noahlessard/2040Listener/main_host.c

/*
 * The MIT License (MIT)
 *
 * Copyright (c) 2019 Ha Thach (tinyusb.org)
 *                    sekigon-gonnoc
 *
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
 */

// This example runs both host and device concurrently. The USB host receive
// reports from HID device and print it out over USB Device CDC interface.
// For TinyUSB roothub port0 is native usb controller, roothub port1 is
// pico-pio-usb.

#include <stdlib.h>
#include <stdio.h>
#include <string.h>

#include "pico/stdlib.h"
#include "pico/multicore.h"
#include "pico/bootrom.h"

#include "pio_usb.h"
#include "tusb.h"
#include "usb_descriptors.h"
#include "pico_lfs.h"

#include "pico/util/queue.h"



//--------------------------------------------------------------------+
// MACRO CONSTANT TYPEDEF PROTYPES
//--------------------------------------------------------------------+


volatile bool core1_ready = false;
static uint8_t const keycode2ascii[128][2] =  { HID_KEYCODE_TO_ASCII };
extern queue_t keypress_queue;

/*------------- MAIN -------------*/

// core1: handle host events
void core1_main() {
  sleep_ms(10);

  // need to allow this core to be paused by core0! Otherwise LFS won't work
  multicore_lockout_victim_init();
  core1_ready = true;  

  // Use tuh_configure() to pass pio configuration to the host stack
  // Note: tuh_configure() must be called before
  pio_usb_configuration_t pio_cfg = {
    .pin_dp = PIO_USB_DP_PIN_DEFAULT,
    .pio_tx_num = PIO_USB_TX_DEFAULT,
    .sm_tx = PIO_SM_USB_TX_DEFAULT,
    .tx_ch = PIO_USB_DMA_TX_DEFAULT,
    .pio_rx_num = PIO_USB_RX_DEFAULT,
    .sm_rx = PIO_SM_USB_RX_DEFAULT,
    .sm_eop = PIO_SM_USB_EOP_DEFAULT,
    .alarm_pool = NULL, // Set to your alarm pool if you have one, otherwise NULL
    .debug_pin_rx = PIO_USB_DEBUG_PIN_NONE,
    .debug_pin_eop = PIO_USB_DEBUG_PIN_NONE,
    .skip_alarm_pool = false, // Add this line, typically false if using alarm_pool
    .pinout = PIO_USB_PINOUT_DPDM // Add this line, as per newer pio_usb.h
};
  tuh_configure(1, TUH_CFGID_RPI_PIO_USB_CONFIGURATION, &pio_cfg);

  // To run USB SOF interrupt in core1, init host stack for pio_usb (roothub
  // port1) on core1
  tuh_init(1);

  while (true) {
    tuh_task(); // tinyusb host task, process all data coming from keyboard
  }
}

//--------------------------------------------------------------------+
// Host HID
//--------------------------------------------------------------------+

// Invoked when device with hid interface is mounted
// Report descriptor is also available for use. tuh_hid_parse_report_descriptor()
// can be used to parse common/simple enough descriptor.
// Note: if report descriptor length > CFG_TUH_ENUMERATION_BUFSIZE, it will be skipped
// therefore report_desc = NULL, desc_len = 0
void tuh_hid_mount_cb(uint8_t dev_addr, uint8_t instance, uint8_t const* desc_report, uint16_t desc_len)
{
  (void)desc_report;
  (void)desc_len;

  // Interface protocol (hid_interface_protocol_enum_t)
  const char* protocol_str[] = { "None", "Keyboard", "Mouse" };
  uint8_t const itf_protocol = tuh_hid_interface_protocol(dev_addr, instance);

  uint16_t vid, pid;
  tuh_vid_pid_get(dev_addr, &vid, &pid);

  char tempbuf[256];
  int count = sprintf(tempbuf, "[%04x:%04x][%u] HID Interface%u, Protocol = %s\r\n", vid, pid, dev_addr, instance, protocol_str[itf_protocol]);

  tud_cdc_write(tempbuf, count);
  tud_cdc_write_flush();

  // Receive report from boot keyboard & mouse only
  // tuh_hid_report_received_cb() will be invoked when report is available
  if (itf_protocol == HID_ITF_PROTOCOL_KEYBOARD || itf_protocol == HID_ITF_PROTOCOL_MOUSE)
  {
    if ( !tuh_hid_receive_report(dev_addr, instance) )
    {
      tud_cdc_write_str("Error: cannot request report\r\n");
    }
  }
}

// Invoked when device with hid interface is un-mounted
void tuh_hid_umount_cb(uint8_t dev_addr, uint8_t instance)
{
  char tempbuf[256];
  int count = sprintf(tempbuf, "[%u] HID Interface%u is unmounted\r\n", dev_addr, instance);
  tud_cdc_write(tempbuf, count);
  tud_cdc_write_flush();
}

// look up new key in previous keys
static inline bool find_key_in_report(hid_keyboard_report_t const *report, uint8_t keycode)
{
  for(uint8_t i=0; i<6; i++)
  {
    if (report->keycode[i] == keycode)  return true;
  }

  return false;
}


// convert hid keycode to ascii and print via usb device CDC (ignore non-printable)
static void process_kbd_report(uint8_t dev_addr, hid_keyboard_report_t const *report)
{
  (void) dev_addr;
  static hid_keyboard_report_t prev_report = { 0, 0, {0} }; // previous report to check key released
  bool flush = false;

  // send keyboard report data to real host, via tud task (which is in core0)
  tud_hid_keyboard_report(REPORT_ID_KEYBOARD, report->modifier, (uint8_t*) report->keycode);
  
  for(uint8_t i=0; i<6; i++)
  {
    uint8_t keycode = report->keycode[i];
    if ( keycode )
    {
      if ( find_key_in_report(&prev_report, keycode) )
      {
        // exist in previous report means the current key is holding
      }else
      {
        // not existed in previous report means the current key is pressed

        bool const is_shift = report->modifier & (KEYBOARD_MODIFIER_LEFTSHIFT | KEYBOARD_MODIFIER_RIGHTSHIFT);
        uint8_t ch = keycode2ascii[keycode][is_shift ? 1 : 0];

        if (ch)
        {
          queue_try_add(&keypress_queue, &ch);
          if (ch == '\n') tud_cdc_write("\r", 1);
          // also, write to cdc for logging, which will be sent in core0
          //tud_cdc_write(&ch, 1);
          flush = true;

        }
      }
    }
    // TODO example skips key released
  }

  if (flush) tud_cdc_write_flush();

  prev_report = *report;
}

// send mouse report to usb device CDC
static void process_mouse_report(uint8_t dev_addr, hid_mouse_report_t const * report)
{
  tud_hid_mouse_report(REPORT_ID_MOUSE, report->buttons, report->x, report->y, report->wheel, 0);

  //------------- button state  -------------//
  //uint8_t button_changed_mask = report->buttons ^ prev_report.buttons;
  char l = report->buttons & MOUSE_BUTTON_LEFT   ? 'L' : '-';
  char m = report->buttons & MOUSE_BUTTON_MIDDLE ? 'M' : '-';
  char r = report->buttons & MOUSE_BUTTON_RIGHT  ? 'R' : '-';
  char f = report->buttons & MOUSE_BUTTON_FORWARD  ? 'F' : '-';
  char b = report->buttons & MOUSE_BUTTON_BACKWARD  ? 'B' : '-';

  char tempbuf[32];
  int count = sprintf(tempbuf, "[%u] %c%c%c%c%c %d %d %d\r\n", dev_addr, l, m, r, f, b, report->x, report->y, report->wheel);

  tud_cdc_write(tempbuf, count);
  tud_cdc_write_flush();
}

// Invoked when received report from device via interrupt endpoint
void tuh_hid_report_received_cb(uint8_t dev_addr, uint8_t instance, uint8_t const* report, uint16_t len)
{
  (void) len;
  uint8_t const itf_protocol = tuh_hid_interface_protocol(dev_addr, instance);

  // Print raw report bytes for debugging
  /*char raw_report_buf[len * 3 + 1]; // Each byte takes 2 hex chars + space, plus null terminator
  int offset = 0;
  for (uint16_t i = 0; i < len; i++) {
    offset += sprintf(raw_report_buf + offset, "%02X ", report[i]);
  }
  sprintf(raw_report_buf + offset, "\r\n");
  tud_cdc_write("Raw HID report: ", 16);
  tud_cdc_write(raw_report_buf, strlen(raw_report_buf));
  tud_cdc_write_flush();*/

  switch(itf_protocol)
  {
    case HID_ITF_PROTOCOL_KEYBOARD:
      process_kbd_report(dev_addr, (hid_keyboard_report_t const*) report );
    break;

    case HID_ITF_PROTOCOL_MOUSE:
      process_mouse_report(dev_addr, (hid_mouse_report_t const*) report );
    break;

    default: break;
  }

  // continue to request to receive report
  if ( !tuh_hid_receive_report(dev_addr, instance) )
  {
    tud_cdc_write_str("Error: cannot request report\r\n");
  }
}
